psobot/musicboy/code/cart_emulation.h

/**
  ******************************************************************************
  * @file    TIM_TimeBase/stm32f4xx_it.h
  * @author  MCD Application Team
  * @version V1.0.0
  * @date    19-September-2011
  * @brief   This file contains the headers of the interrupt handlers.
  ******************************************************************************
  * @attention
  *
  * THE PRESENT FIRMWARE WHICH IS FOR GUIDANCE ONLY AIMS AT PROVIDING CUSTOMERS
  * WITH CODING INFORMATION REGARDING THEIR PRODUCTS IN ORDER FOR THEM TO SAVE
  * TIME. AS A RESULT, STMICROELECTRONICS SHALL NOT BE HELD LIABLE FOR ANY
  * DIRECT, INDIRECT OR CONSEQUENTIAL DAMAGES WITH RESPECT TO ANY CLAIMS ARISING
  * FROM THE CONTENT OF SUCH FIRMWARE AND/OR THE USE MADE BY CUSTOMERS OF THE
  * CODING INFORMATION CONTAINED HEREIN IN CONNECTION WITH THEIR PRODUCTS.
  *
  * <h2><center>&copy; COPYRIGHT 2011 STMicroelectronics</center></h2>
  ******************************************************************************
  */

/* Define to prevent recursive inclusion -------------------------------------*/
#ifndef __STM32F4xx_IT_H
#define __STM32F4xx_IT_H

/* Includes ------------------------------------------------------------------*/
#include "lib/stm32f4xx.h"

/* Exported types ------------------------------------------------------------*/
/* Exported constants --------------------------------------------------------*/
/* Exported macro ------------------------------------------------------------*/
/* Exported functions ------------------------------------------------------- */

void NMI_Handler(void);
void HardFault_Handler(void);
void MemManage_Handler(void);
void BusFault_Handler(void);
void UsageFault_Handler(void);
void SVC_Handler(void);
void DebugMon_Handler(void);
void PendSV_Handler(void);
void SysTick_Handler(void);
void TIM3_IRQHandler(void);

extern uint8_t SHARED_MEMORY[4096];
enum Device { Unknown, DMG, CGB };
extern volatile enum Device device;

#endif /* __STM32F4xx_IT_H */

/******************* (C) COPYRIGHT 2011 STMicroelectronics *****END OF FILE****/
